yzhou30-ux/514-FinalProject/enclosure/_ (30).jpeg

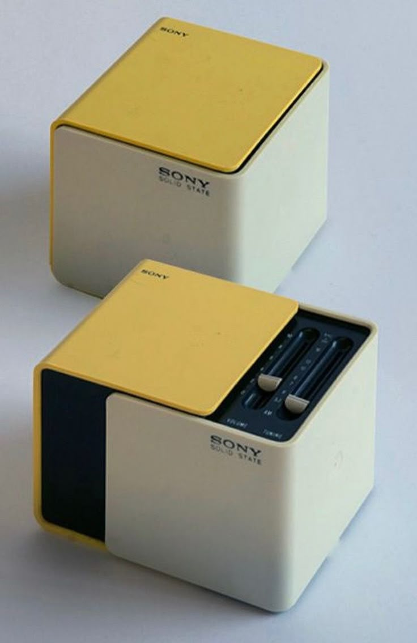
enclosure/_ (30).jpeg
