yzhou30-ux/514-FinalProject/enclosure/_ (31).jpeg

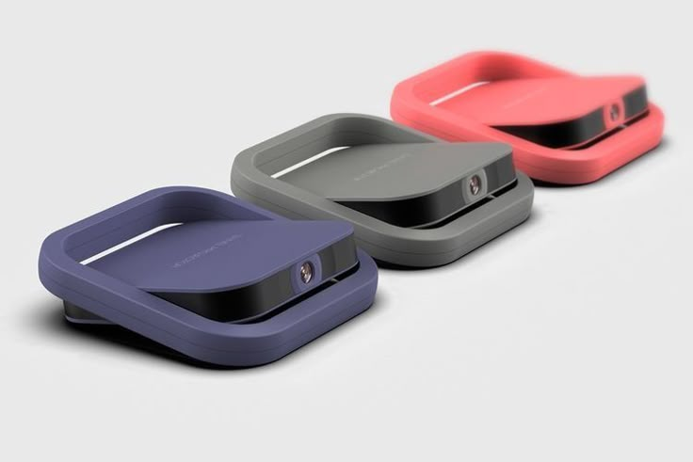
enclosure/_ (31).jpeg
