yzhou30-ux/514-FinalProject/enclosure/IMG_5771.JPG

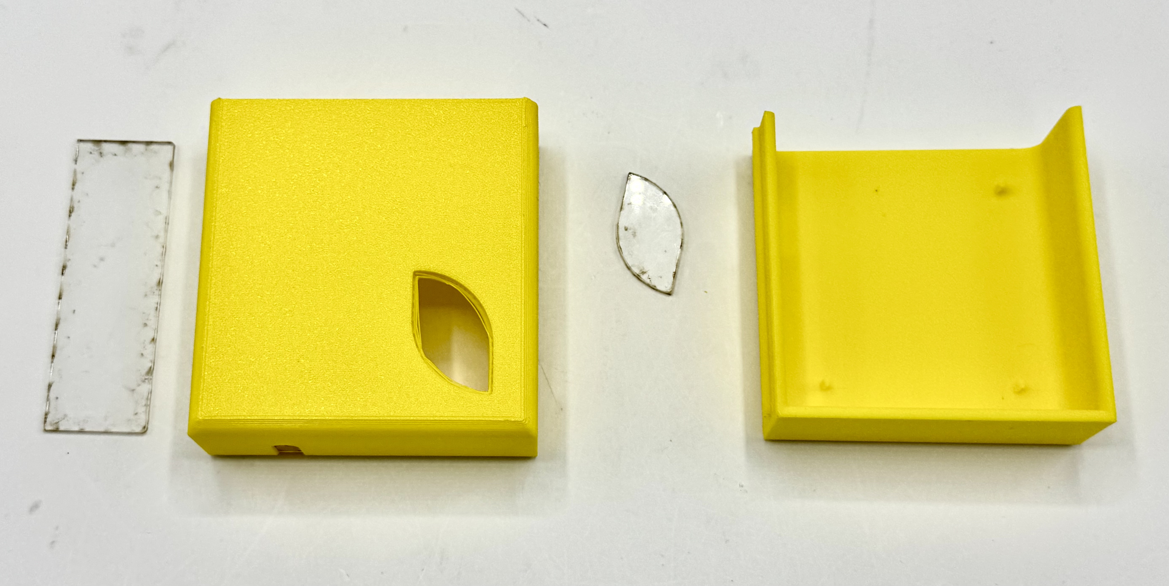
enclosure/IMG_5771.JPG
