yzhou30-ux/514-FinalProject/enclosure/IMG_5772.JPG

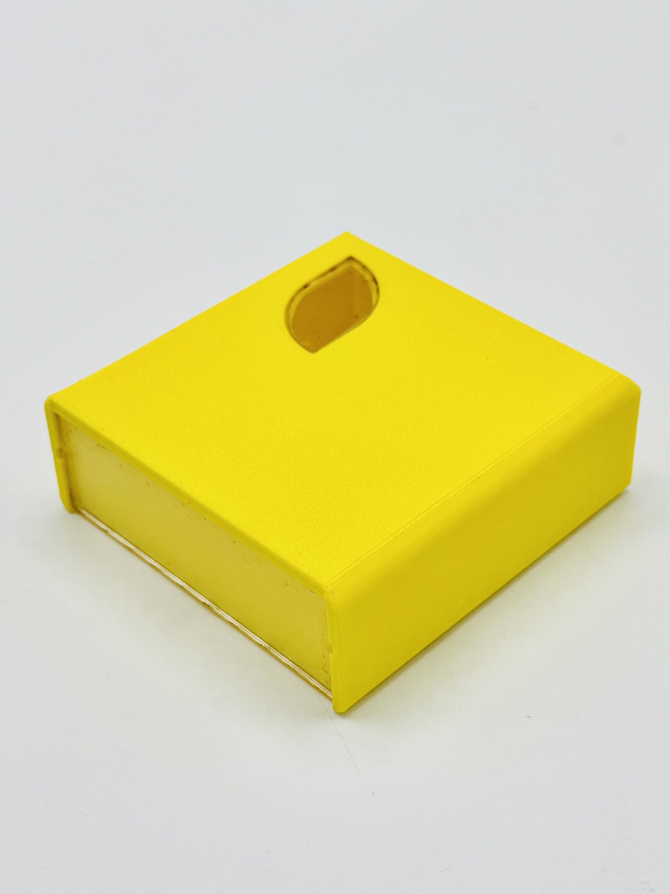
enclosure/IMG_5772.JPG
