yzhou30-ux/514-FinalProject/enclosure/IMG_5773.JPG

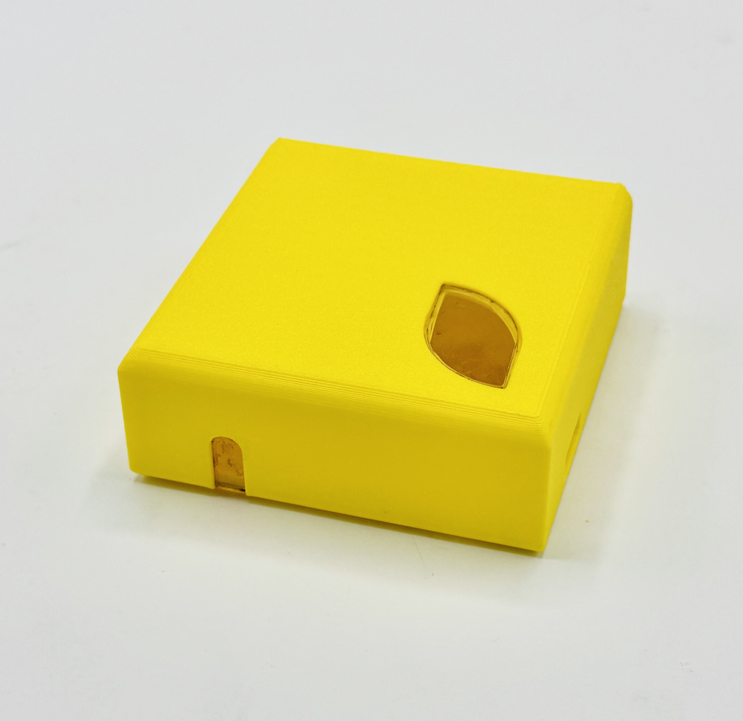
enclosure/IMG_5773.JPG
