yzhou30-ux/514-FinalProject/enclosure/IMG_5774.JPG

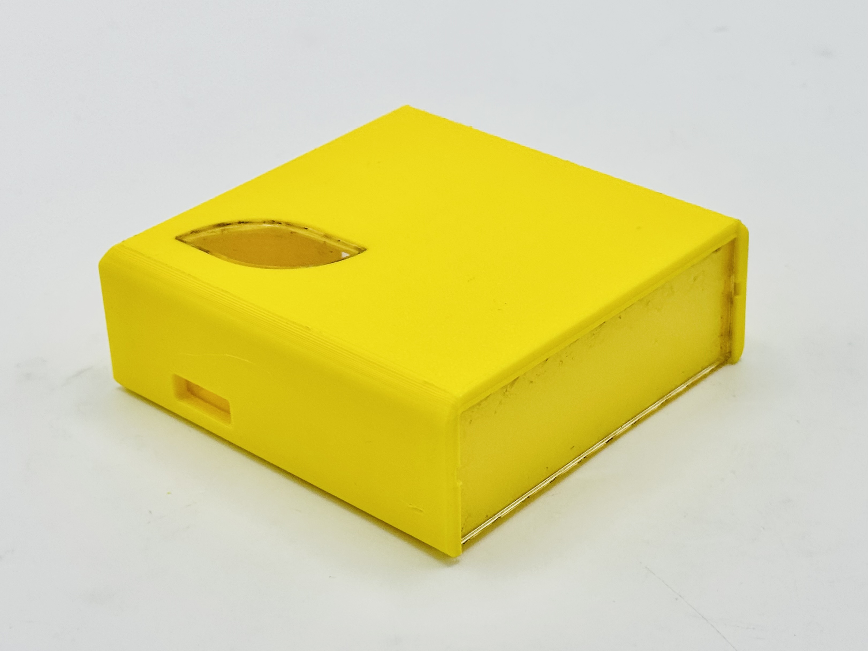
enclosure/IMG_5774.JPG
